ronihdzz/IoT_domotica/GUI/IMAGENES/DEBERES/izquierda.png

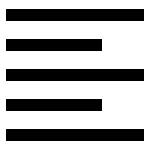
GUI/IMAGENES/DEBERES/izquierda.png
