ronihdzz/IoT_domotica/GUI/IMAGENES/SISTEMA_CONTROL/alertaFuego.png

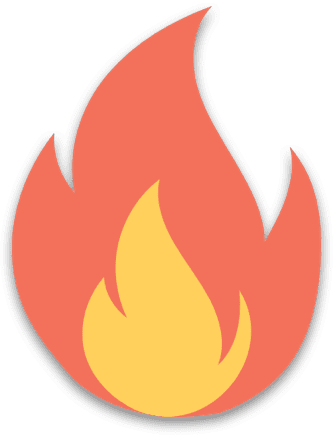
GUI/IMAGENES/SISTEMA_CONTROL/alertaFuego.png
