ronihdzz/IoT_domotica/GUI/IMAGENES/SISTEMA_CONTROL/foco0a_default.png

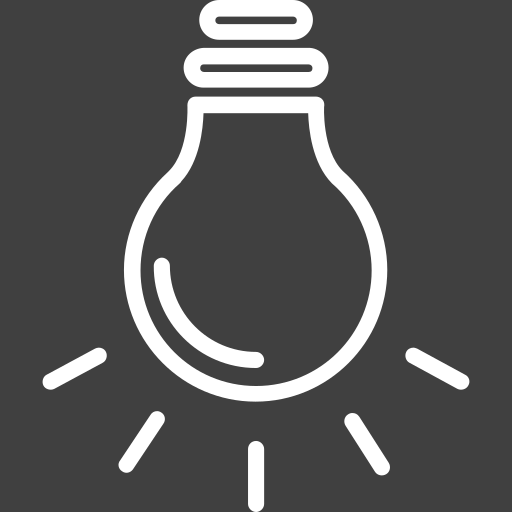
GUI/IMAGENES/SISTEMA_CONTROL/foco0a_default.png
