ronihdzz/IoT_domotica/GUI/IMAGENES/SISTEMA_CONTROL/foco0b_default.png

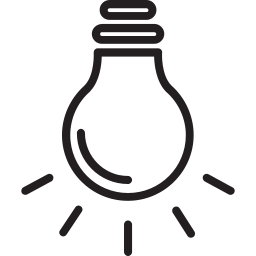
GUI/IMAGENES/SISTEMA_CONTROL/foco0b_default.png
