ronihdzz/IoT_domotica/GUI/IMAGENES/SISTEMA_CONTROL/foco2_rojo.png

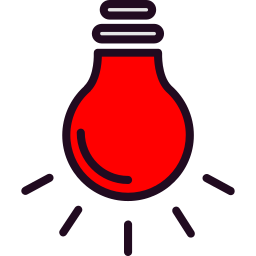
GUI/IMAGENES/SISTEMA_CONTROL/foco2_rojo.png
