ronihdzz/IoT_domotica/GUI/IMAGENES/SISTEMA_CONTROL/rrueda2_rojo.png

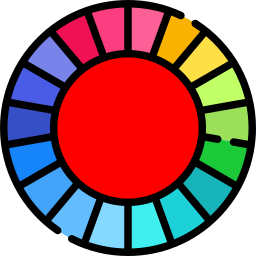
GUI/IMAGENES/SISTEMA_CONTROL/rrueda2_rojo.png
