ronihdzz/IoT_domotica/GUI/IMAGENES/SISTEMA_CONTROL/rrueda4_azul.png

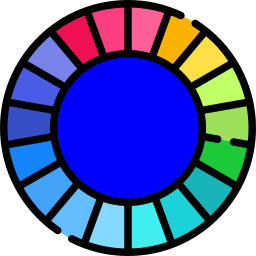
GUI/IMAGENES/SISTEMA_CONTROL/rrueda4_azul.png
