ronihdzz/IoT_domotica/GUI/IMAGENES/SISTEMA_CONTROL/rueda1_blanco.png

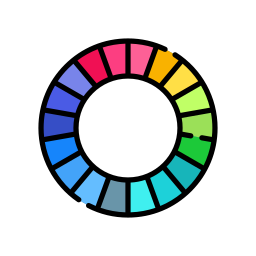
GUI/IMAGENES/SISTEMA_CONTROL/rueda1_blanco.png
