ronihdzz/IoT_domotica/GUI/IMAGENES/SISTEMA_CONTROL/rueda2_rojo.png

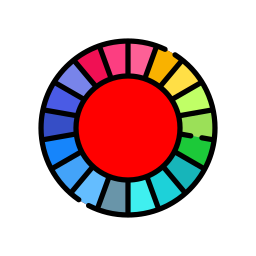
GUI/IMAGENES/SISTEMA_CONTROL/rueda2_rojo.png
