ronihdzz/IoT_domotica/GUI/IMAGENES/SISTEMA_CONTROL/ventilador_on.png

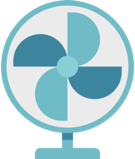
GUI/IMAGENES/SISTEMA_CONTROL/ventilador_on.png
