ronihdzz/IoT_domotica/recursos_readme/OTRO/img3_adaptadorSerieUSB_serial.jpg

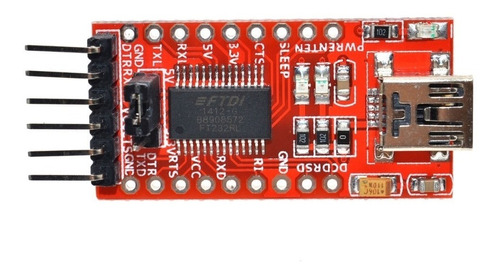
recursos_readme/OTRO/img3_adaptadorSerieUSB_serial.jpg
