ronihdzz/IoT_domotica/recursos_readme/OTRO/img13_cableMicroUSBtoUSB.jpg

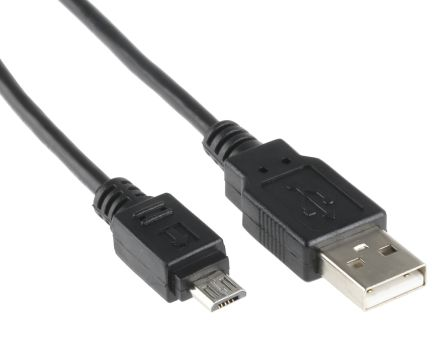
recursos_readme/OTRO/img13_cableMicroUSBtoUSB.jpg
