ronihdzz/IoT_domotica/recursos_readme/OTRO/img15_cabreProtobard.jpg

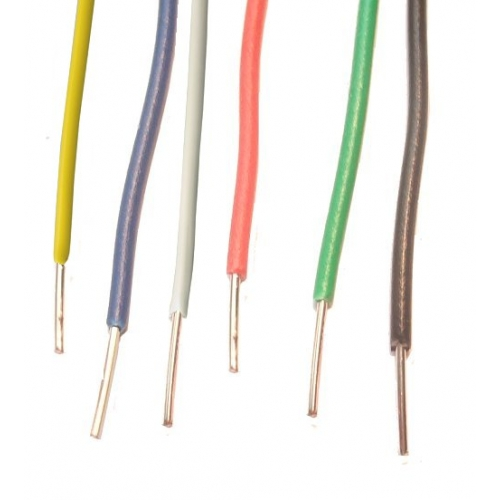
recursos_readme/OTRO/img15_cabreProtobard.jpg
