ronihdzz/IoT_domotica/recursos_readme/SISTEMA_CONTROL/informacion_doble.gif

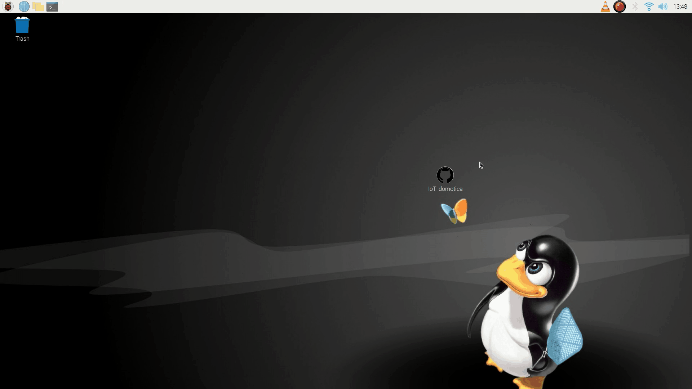
recursos_readme/SISTEMA_CONTROL/informacion_doble.gif
