ronihdzz/IoT_domotica/recursos_readme/SISTEMA_CONTROL/tiposControles2.png

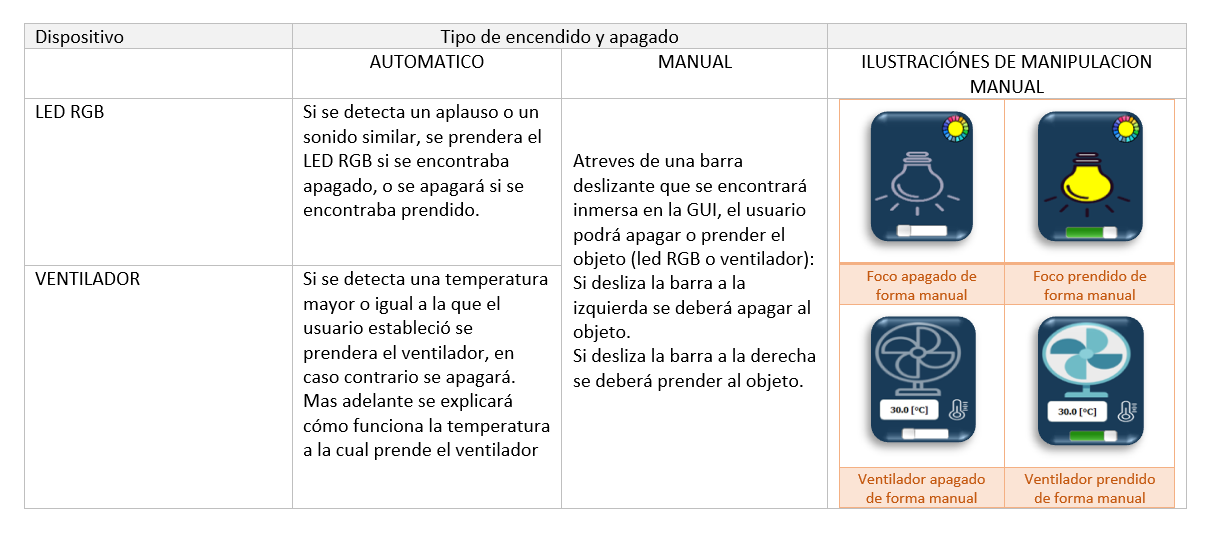
recursos_readme/SISTEMA_CONTROL/tiposControles2.png
