ronihdzz/IoT_domotica/recursos_readme/SISTEMA_CONTROL/tiposControles.png

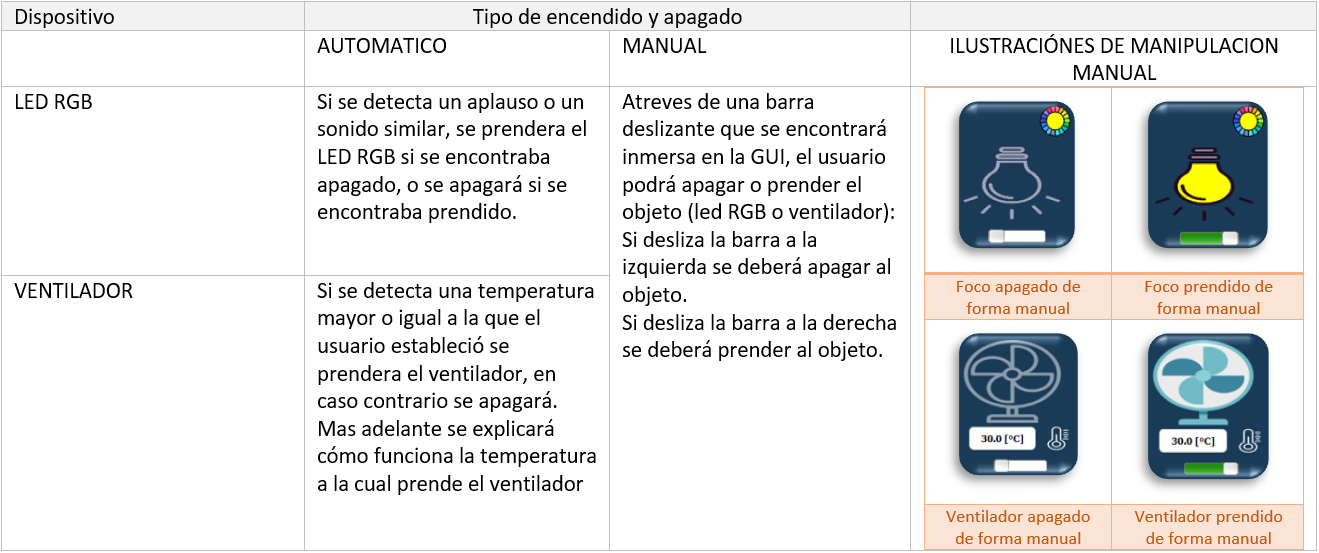
recursos_readme/SISTEMA_CONTROL/tiposControles.png
