ronihdzz/IoT_domotica/HADWARE/scripts_prueba/detectorFlama/detectorFlama.ino

 int led = 5;        // used for ESP32
 int Fire_analog = 2;    // used for ESP32
 int Fire_digital = 4;   // used for ESP32

void setup() {
  Serial.begin(115200);
  pinMode(led, OUTPUT);      
  pinMode(Fire_digital, INPUT);
}

void loop() {
  int firesensorAnalog = analogRead(Fire_analog);
  int firesensorDigital = digitalRead(Fire_digital);

  Serial.print("Fire Sensor: ");
  Serial.print(firesensorAnalog);
  Serial.print("\t");
  Serial.print("Fire Class: ");
  Serial.print(firesensorDigital);
  Serial.print("\t");
  Serial.print("\t");
  
  if (firesensorAnalog < 1000) {
    Serial.println("Fire");
    digitalWrite (led, HIGH) ; //send tone
    delay(1000);
    digitalWrite (led, LOW) ;  //no tone
  }
  else {
    Serial.println("No Fire");
  }
  delay(100);
}
